nategri/chernobyl_dice/images/chernobyl_dice.jpg

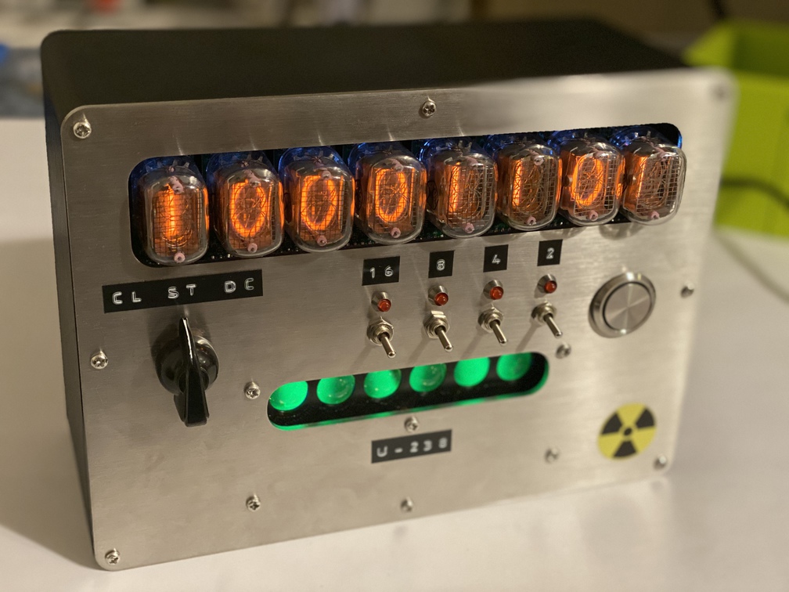
images/chernobyl_dice.jpg
